jalivert/gravity-holder/images/top-no-tube.png

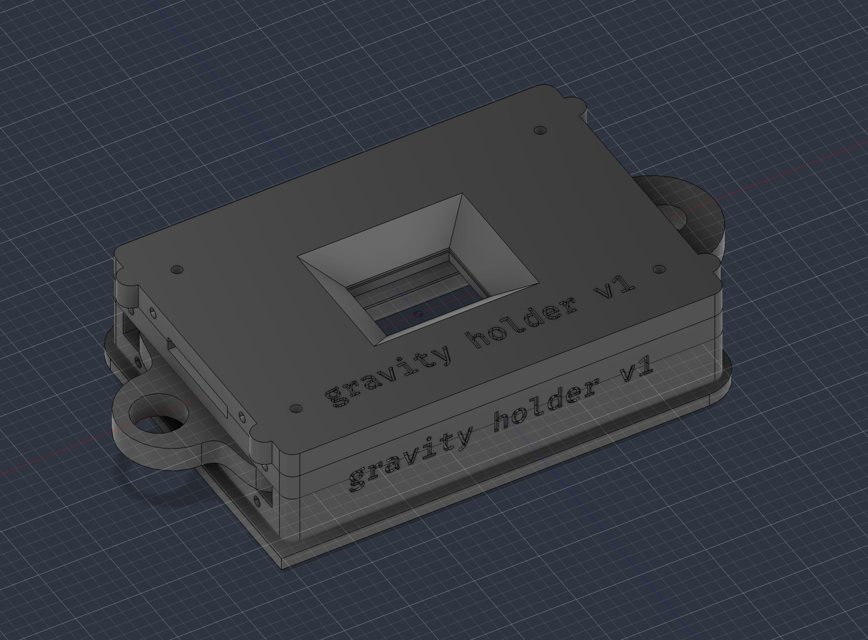
images/top-no-tube.png
